vazeri/ADC-DAC-PCB/img/0.jpg

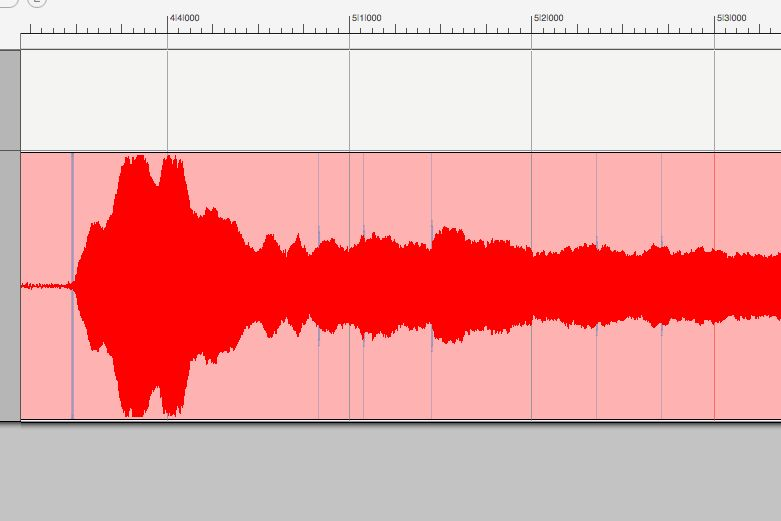
img/0.jpg
