vazeri/ADC-DAC-PCB/img/9.jpg

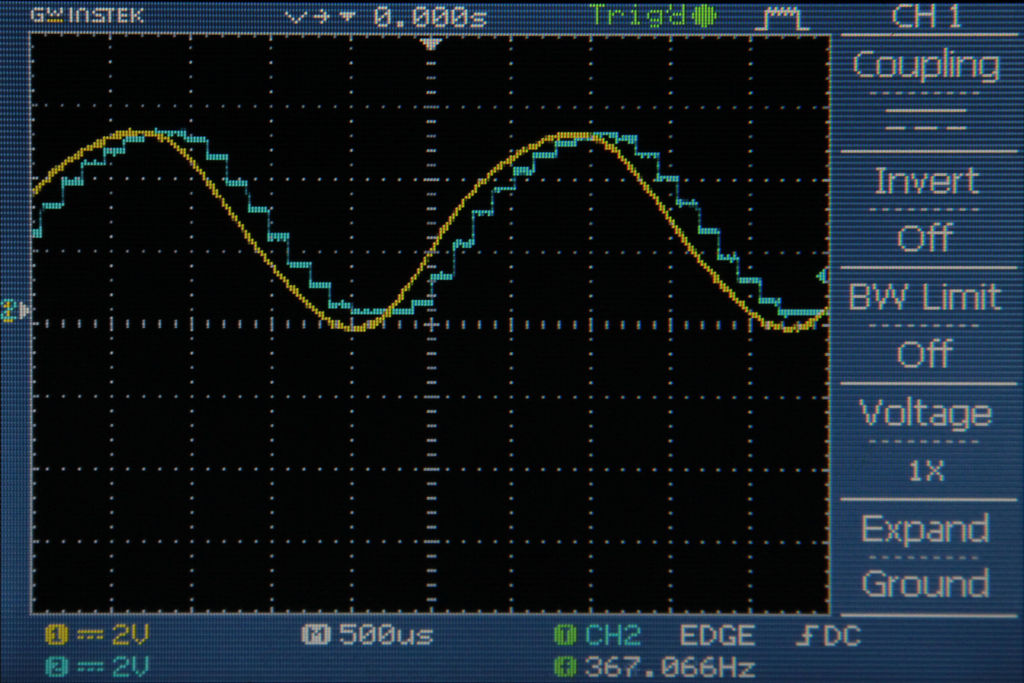
img/9.jpg
