vazeri/ADC-DAC-PCB/img/20k.jpg

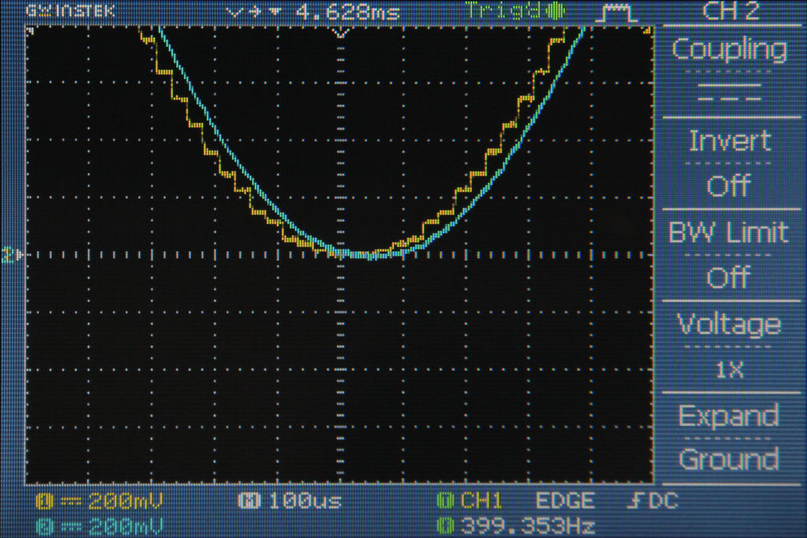
img/20k.jpg
