vazeri/ADC-DAC-PCB/img/23.JPG

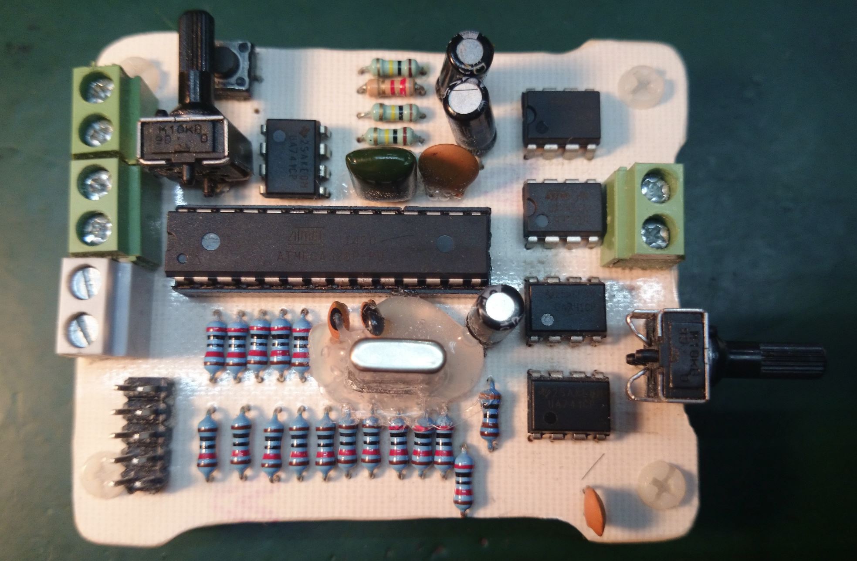
img/23.JPG
