vazeri/ADC-DAC-PCB/img/54.JPG

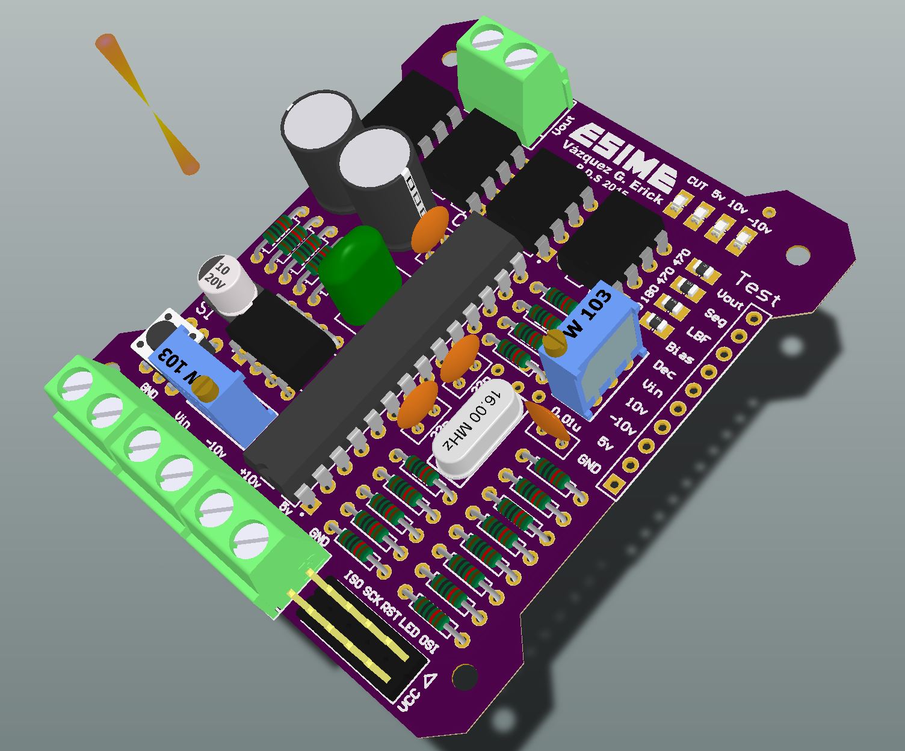
img/54.JPG
