vazeri/ADC-DAC-PCB/img/1234.JPG

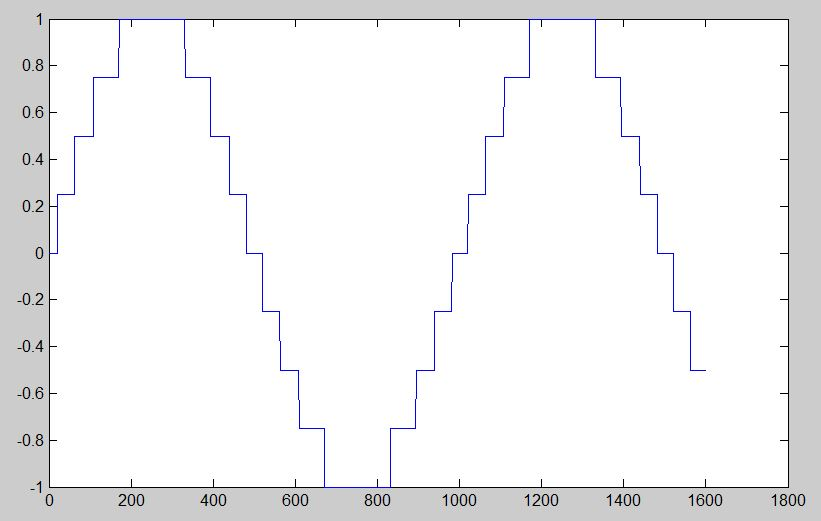
img/1234.JPG
