vazeri/ADC-DAC-PCB/img/2014-11-20 16.28.38.jpg

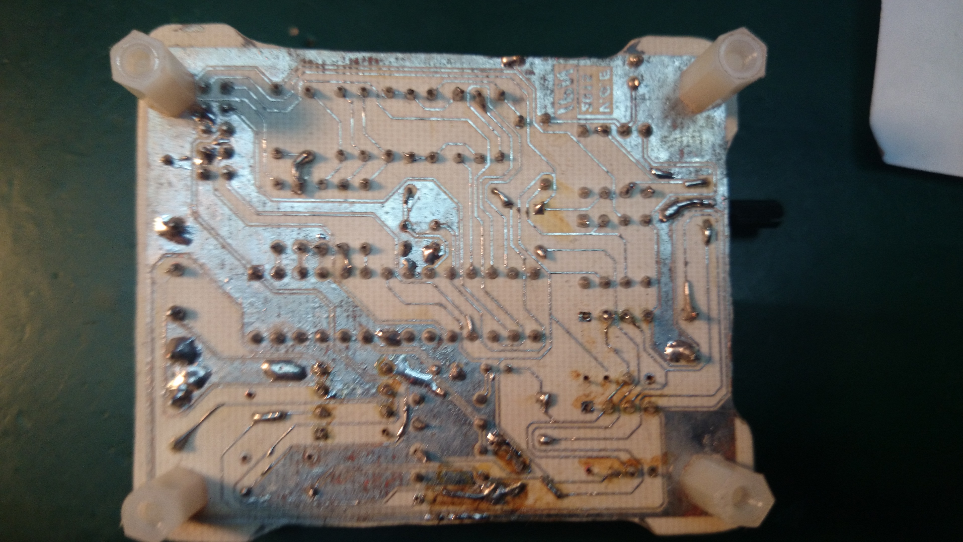
img/2014-11-20 16.28.38.jpg
