vazeri/ADC-DAC-PCB/img/2014-12-18 16.26.15.jpg

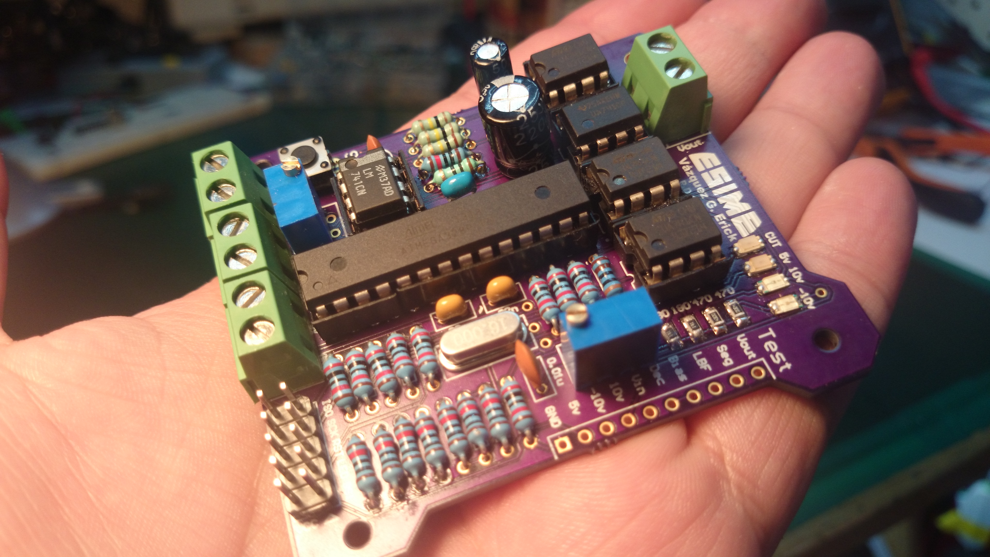
img/2014-12-18 16.26.15.jpg
