vazeri/ADC-DAC-PCB/img/1223312.JPG

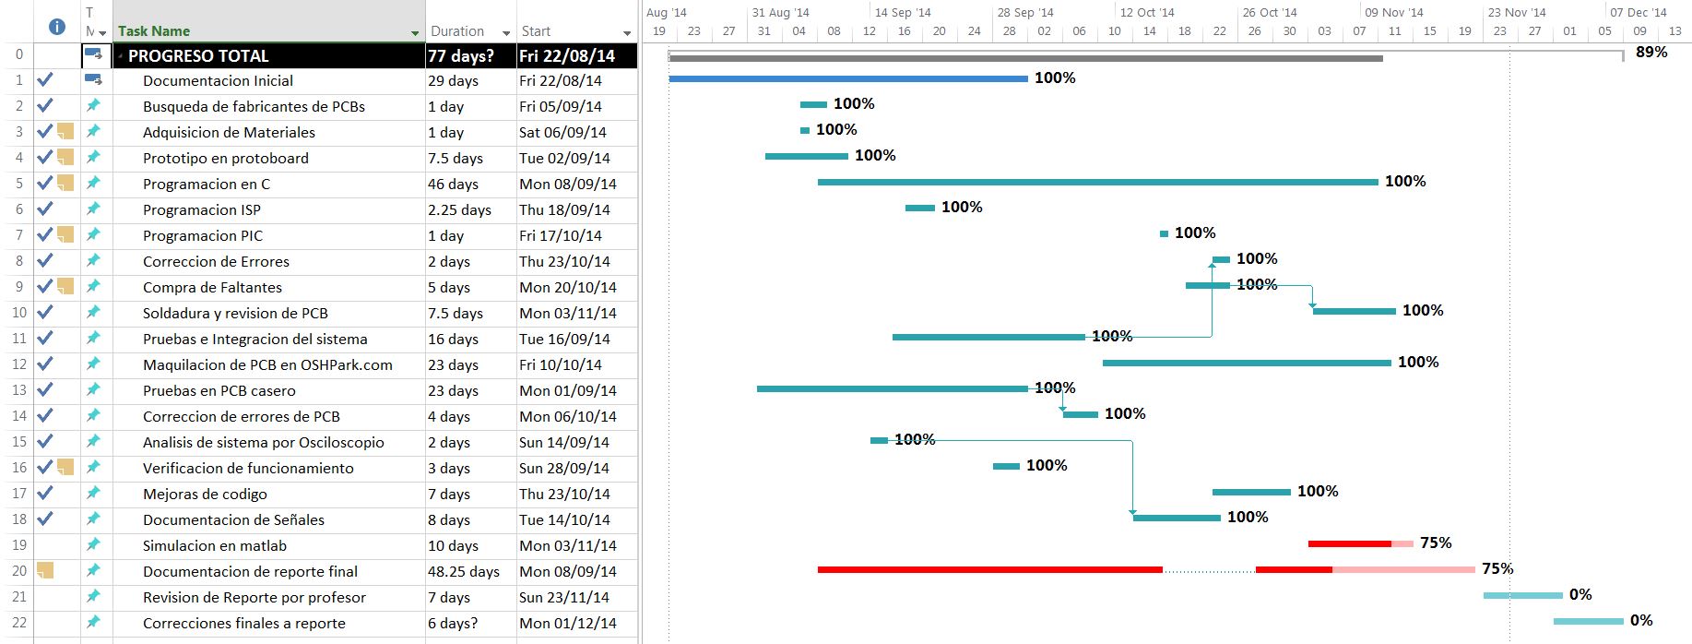
img/1223312.JPG
