vazeri/ADC-DAC-PCB/img/analog.JPG

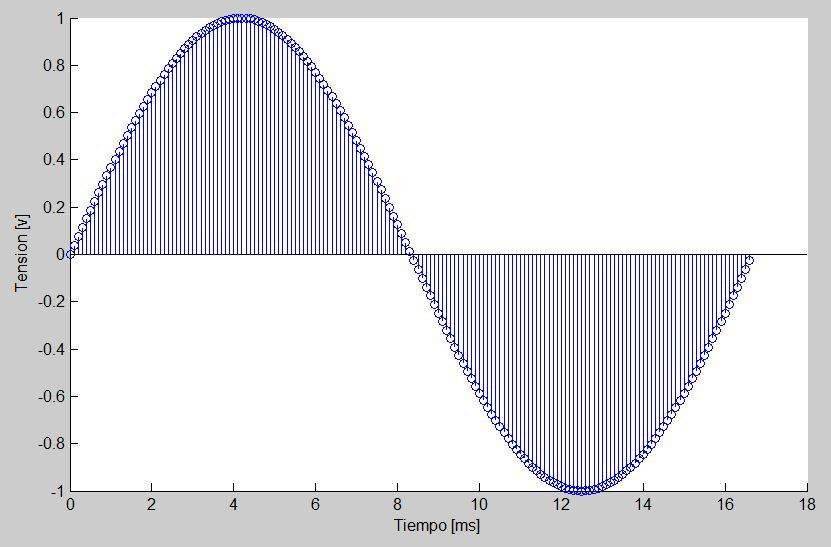
img/analog.JPG
