vazeri/ADC-DAC-PCB/img/AVR.png

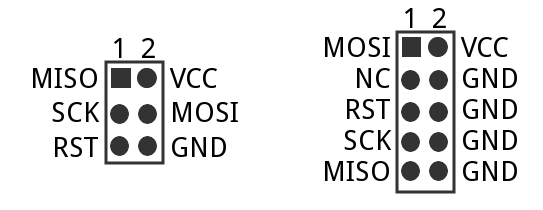
img/AVR.png
