vazeri/ADC-DAC-PCB/img/cto.JPG

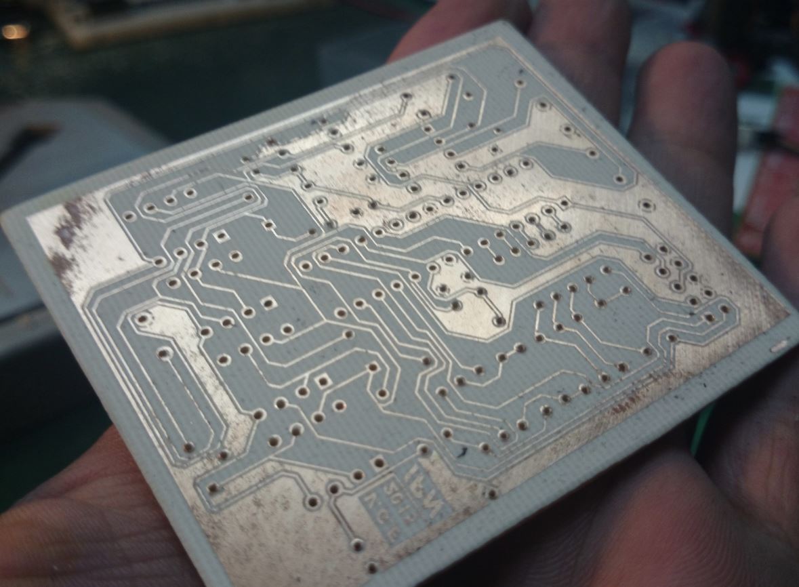
img/cto.JPG
