vazeri/ADC-DAC-PCB/img/dig.JPG

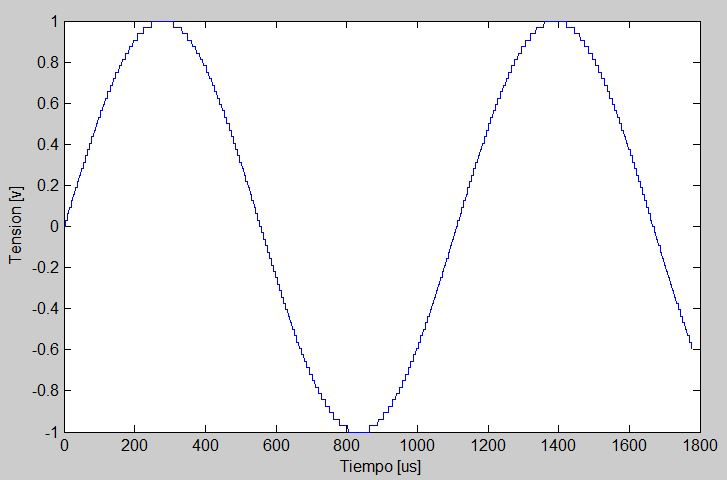
img/dig.JPG
