vazeri/ADC-DAC-PCB/img/IMG-20141107-WA0000.jpeg

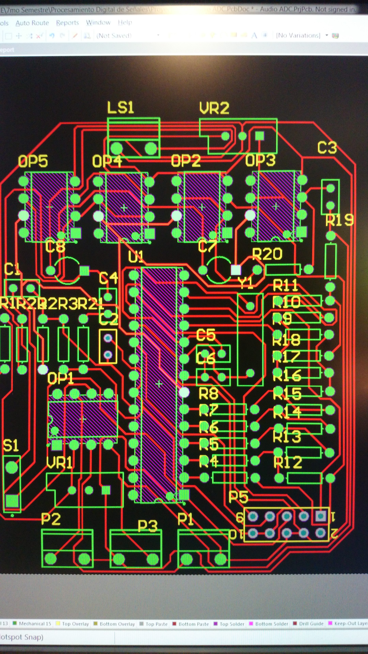
img/IMG-20141107-WA0000.jpeg
