vazeri/ADC-DAC-PCB/img/IMG-20141107-WA0002.jpeg

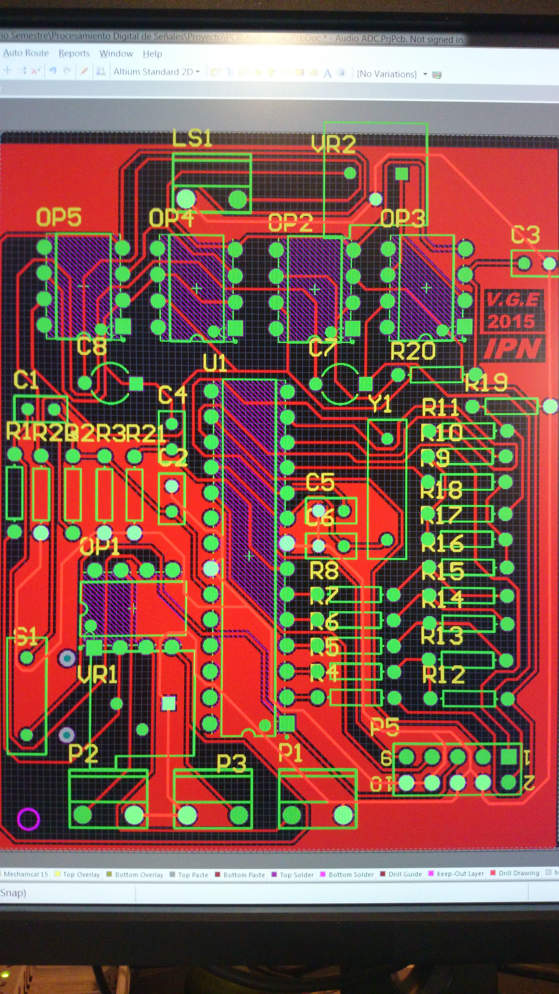
img/IMG-20141107-WA0002.jpeg
