vazeri/ADC-DAC-PCB/img/IMG-20141217-WA0004.jpeg

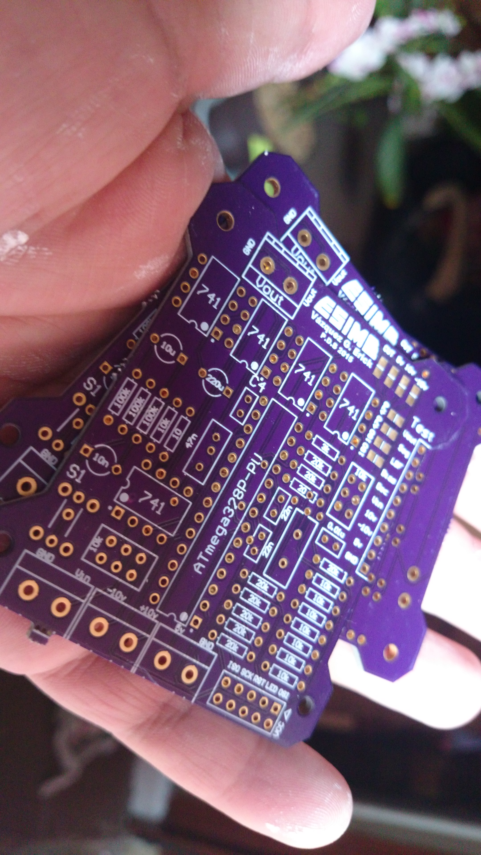
img/IMG-20141217-WA0004.jpeg
