vazeri/ADC-DAC-PCB/img/m2.JPG

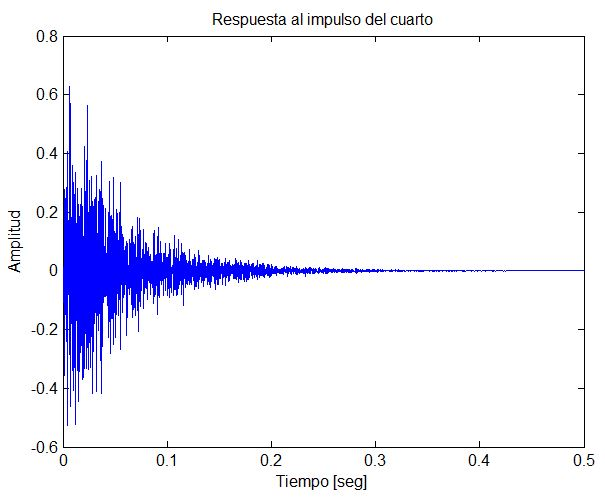
img/m2.JPG
