vazeri/ADC-DAC-PCB/img/m4.JPG

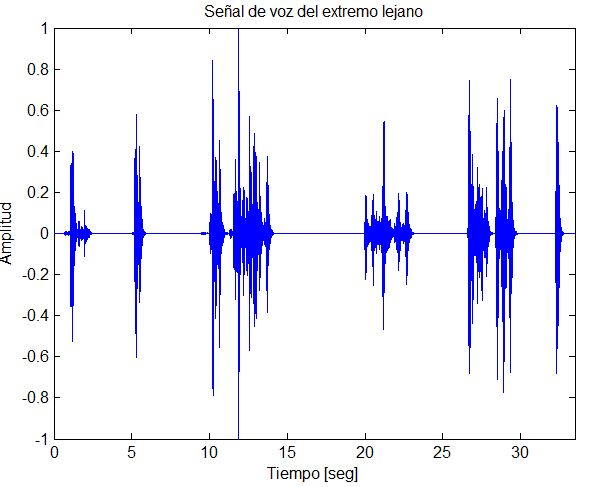
img/m4.JPG
