vazeri/ADC-DAC-PCB/img/m5.JPG

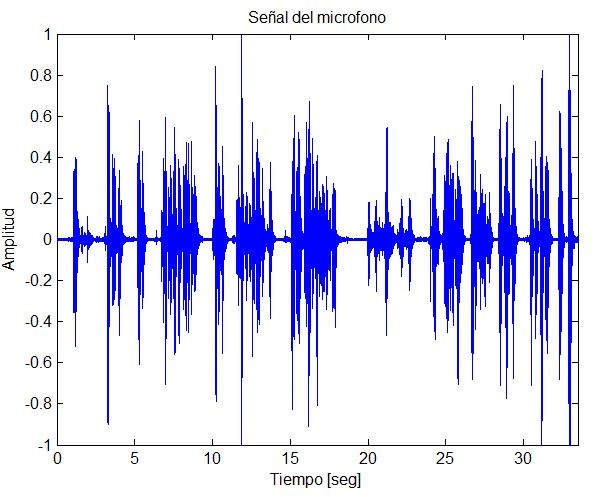
img/m5.JPG
