vazeri/ADC-DAC-PCB/img/m6.JPG

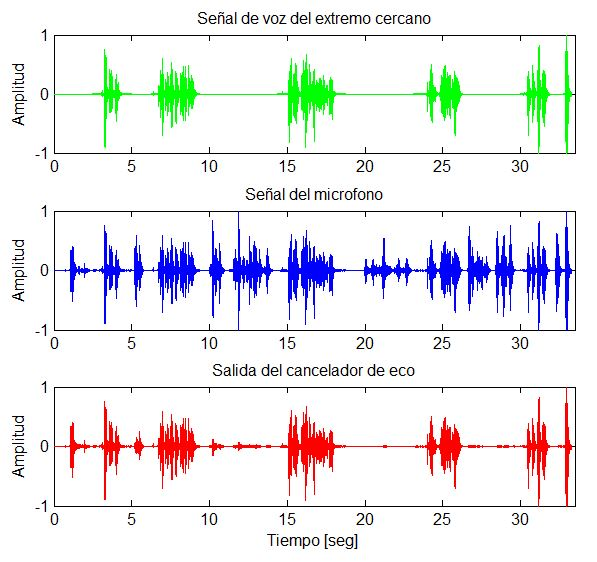
img/m6.JPG
