vazeri/ADC-DAC-PCB/img/m7.JPG

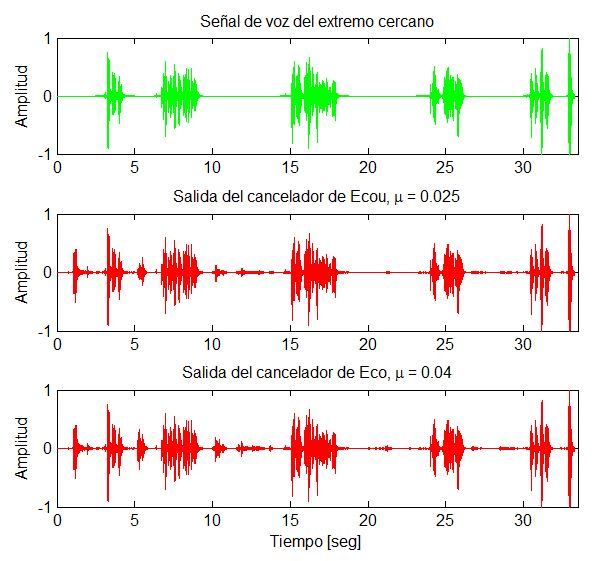
img/m7.JPG
