vazeri/ADC-DAC-PCB/img/m9.JPG

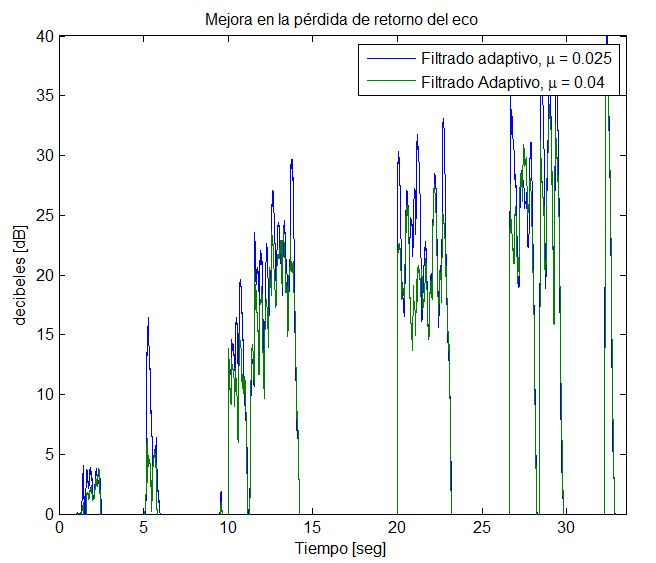
img/m9.JPG
