vazeri/ADC-DAC-PCB/img/mat.JPG

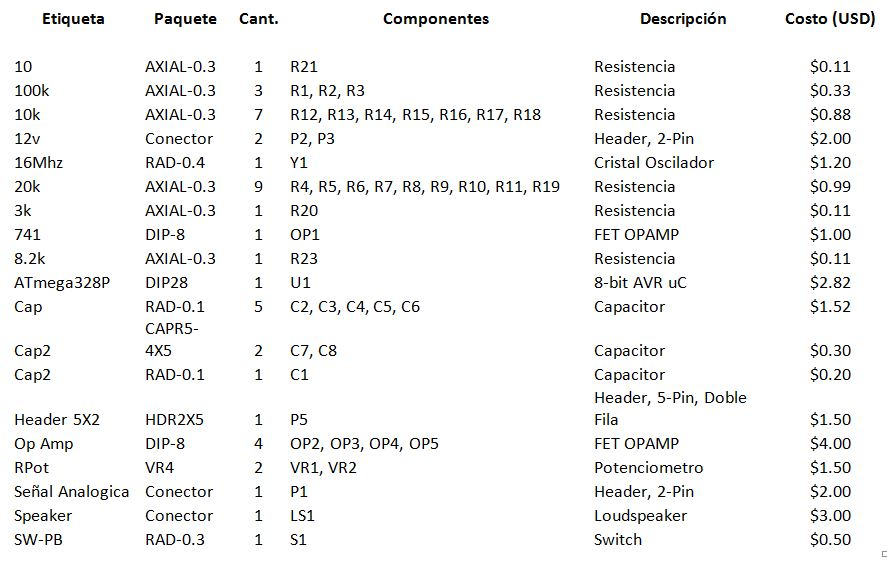
img/mat.JPG
