vazeri/ADC-DAC-PCB/img/mx.JPG

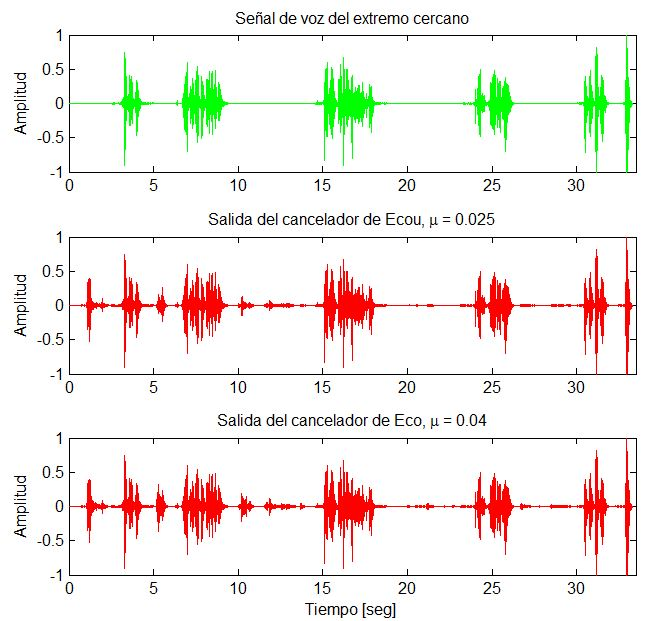
img/mx.JPG
