vazeri/ADC-DAC-PCB/img/offset.jpg

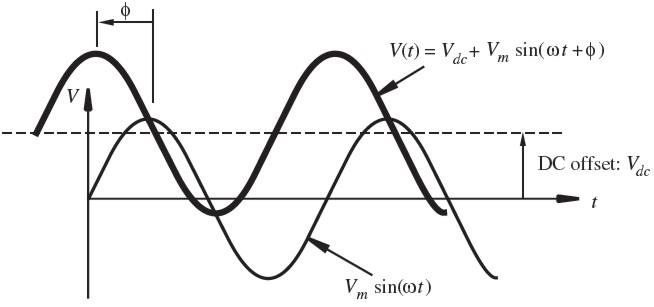
img/offset.jpg
