vazeri/ADC-DAC-PCB/img/PCB.jpg

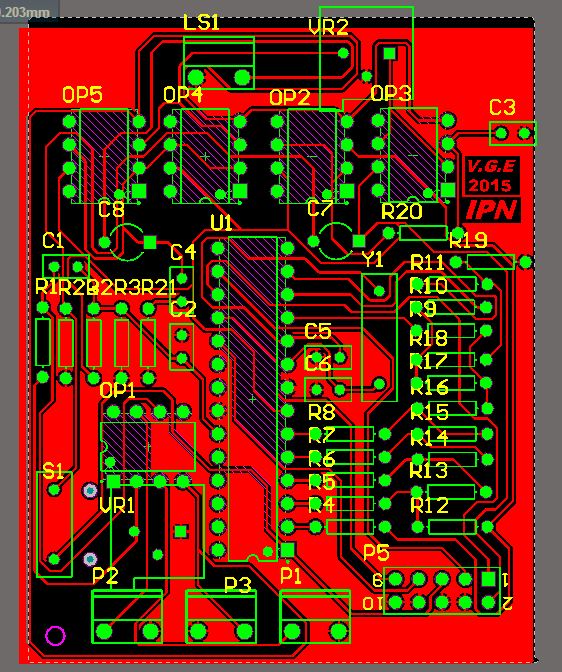
img/PCB.jpg
