vazeri/ADC-DAC-PCB/img/simulacion.jpg

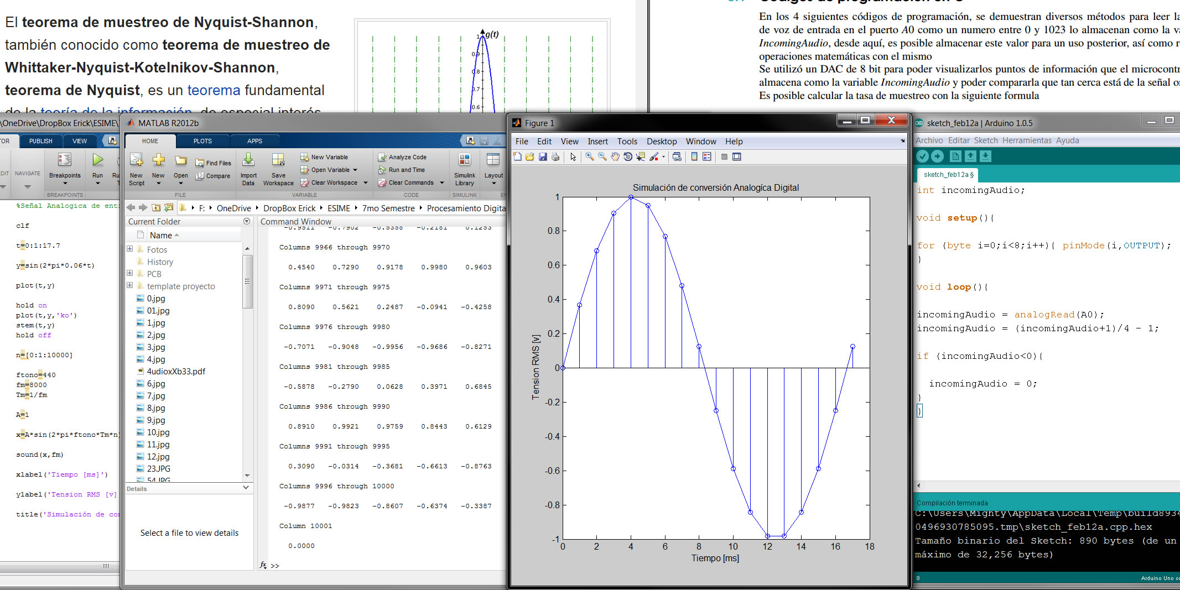
img/simulacion.jpg
