vazeri/ADC-DAC-PCB/img/tarjeta.jpg

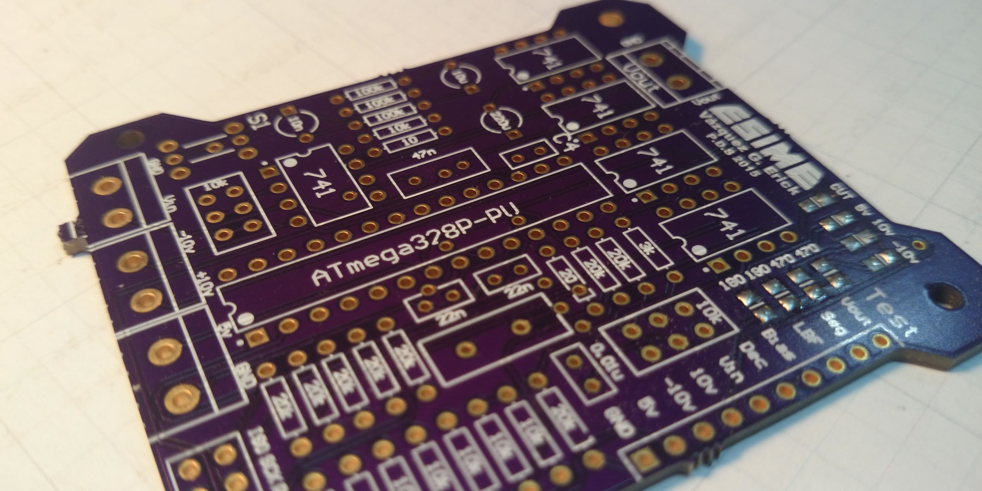
img/tarjeta.jpg
