vazeri/ADC-DAC-PCB/Altium/User Library-LED SMD0805.step

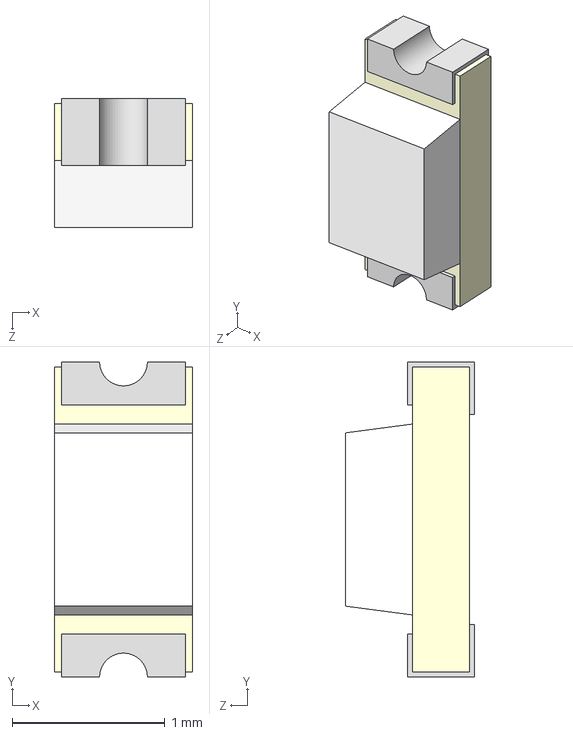
[picture p67: CAD file, 2018-01-22]
Altium/User Library-LED SMD0805.step
0.906 x 2.06 x 0.844 mm
