vazeri/ADC-DAC-PCB/Altium/User Library-Bourns 3362P.step

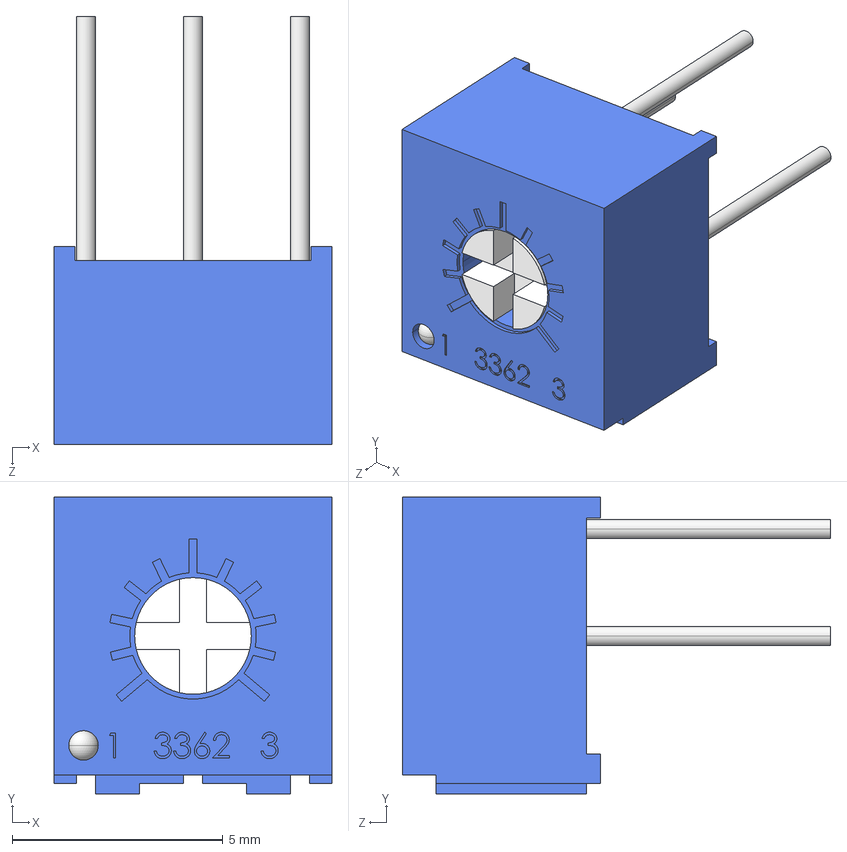
[picture p68: CAD file, 2018-01-22]
Altium/User Library-Bourns 3362P.step
6.60 x 7.05 x 10.2 mm
