vazeri/ADC-DAC-PCB/Altium/User Library-Cap12_5x25.STEP

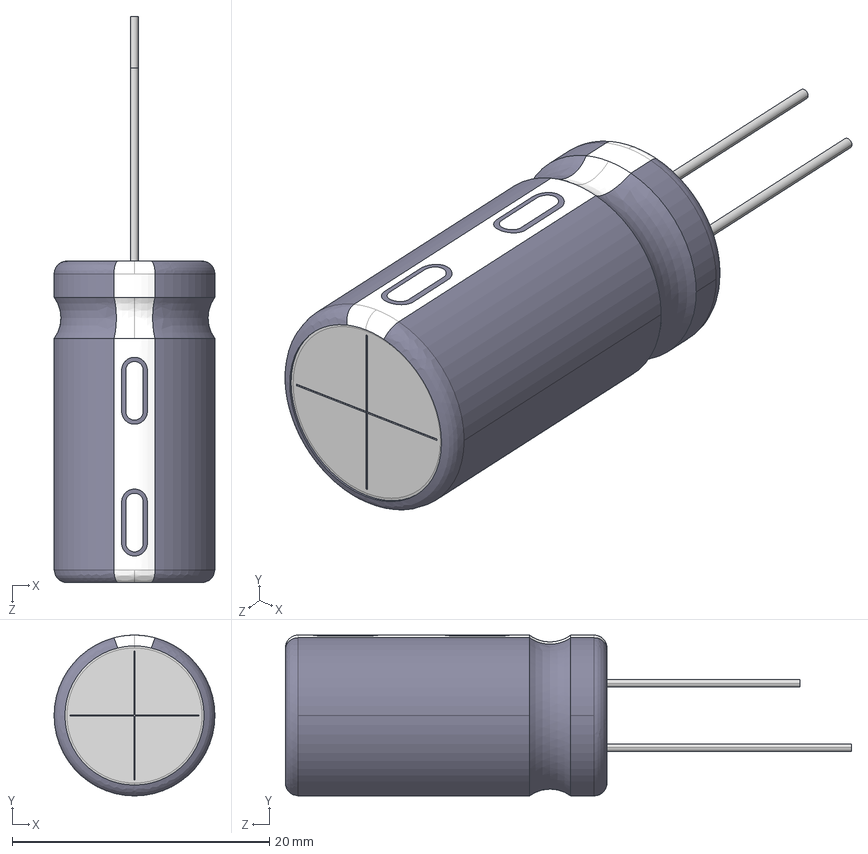
[picture p69: CAD file, 2018-01-22]
Altium/User Library-Cap12_5x25.STEP
12.5 x 12.5 x 44.0 mm
User Library-Cap12.5x25_1_1
User Library-Cap12.5x25_2_1
User Library-Cap12.5x25_3_1
User Library-Cap12.5x25_4_1
User Library-Cap12.5x25_5_1
User Library-Cap12.5x25_6_1
User Library-Cap12.5x25_7_1
User Library-Cap12.5x25_8_1
User Library-Cap12.5x25_9_1
User Library-Cap12.5x25_10_1
