vazeri/ADC-DAC-PCB/Altium/47n.step

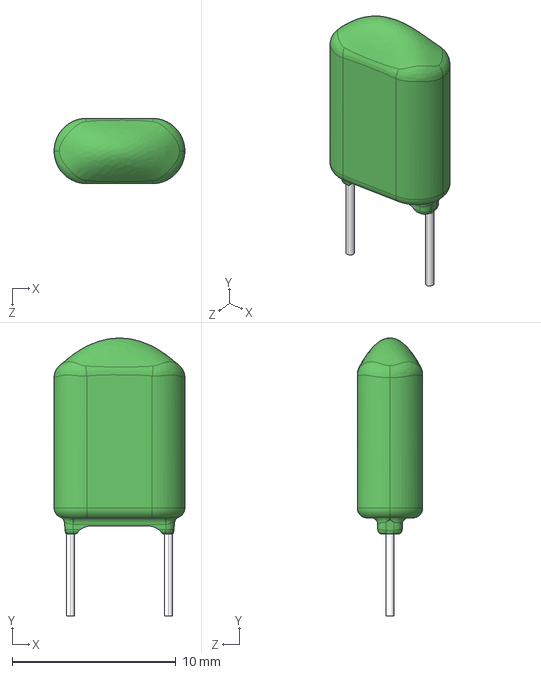
[picture p70: CAD file, 2018-01-22]
Altium/47n.step
8.00 x 17.0 x 4.00 mm
