vazeri/ADC-DAC-PCB/Altium/User Library-DIP8test.STEP

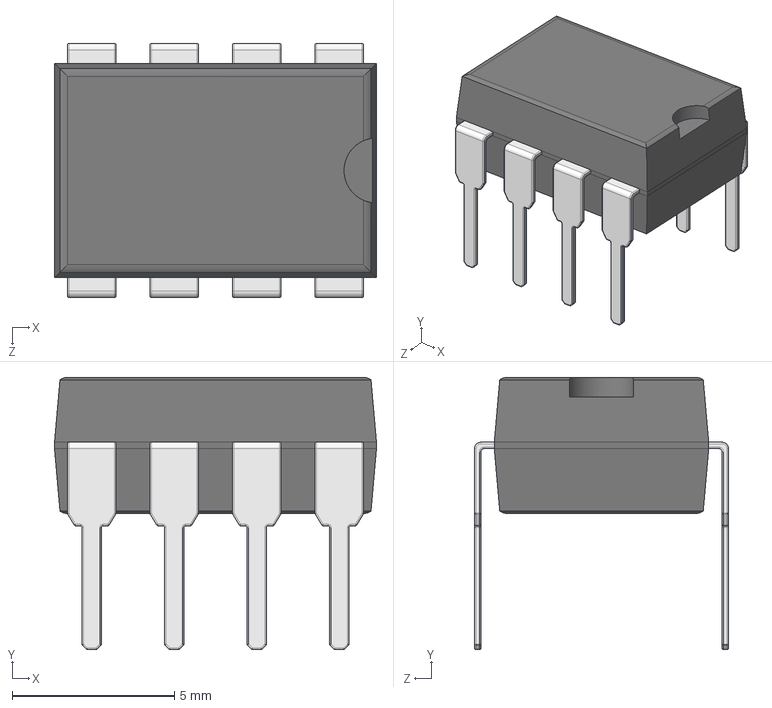
[picture p71: CAD file, 2018-01-22]
Altium/User Library-DIP8test.STEP
9.91 x 8.38 x 7.82 mm
User Library-DIP8test_K_X_F6rper DIP8_1
User Library-DIP8test_Pins Narrow_1 x 8
