vazeri/ADC-DAC-PCB/Altium/Terminal Block.stp

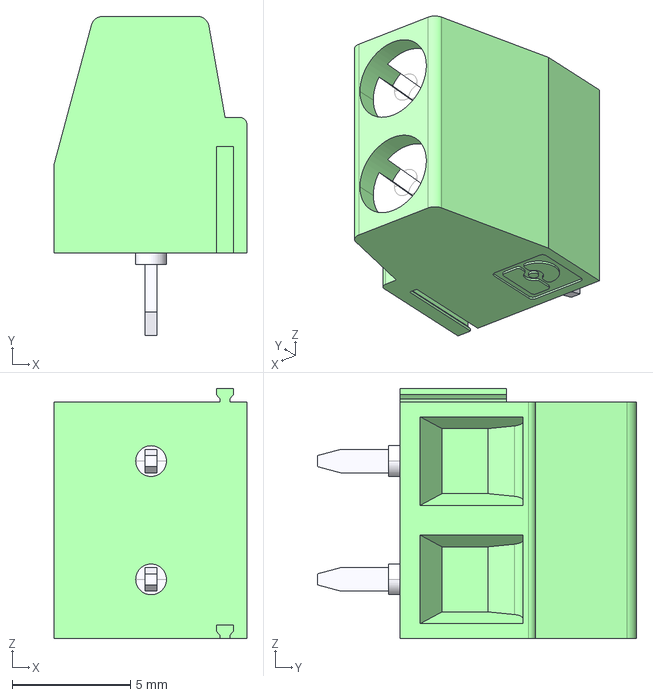
[picture p72: CAD file, 2018-01-22]
Altium/Terminal Block.stp
8.15 x 13.5 x 10.6 mm
