vazeri/ADC-DAC-PCB/Altium/CircuitWorks-REDLED.step

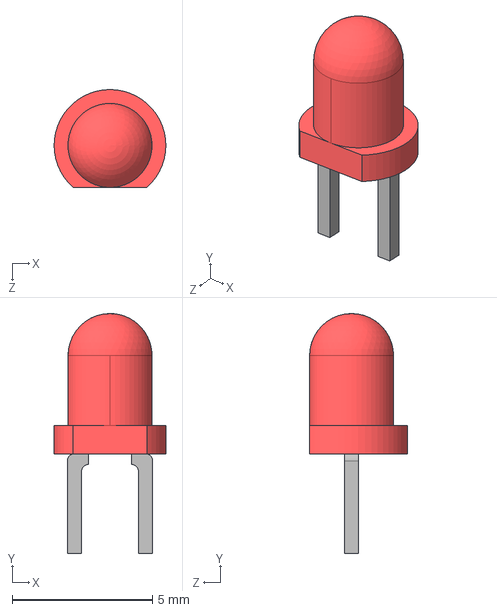
[picture p73: CAD file, 2018-01-22]
Altium/CircuitWorks-REDLED.step
3.99 x 8.56 x 3.49 mm
