vazeri/ADC-DAC-PCB/img/PRUEBAS.jpg

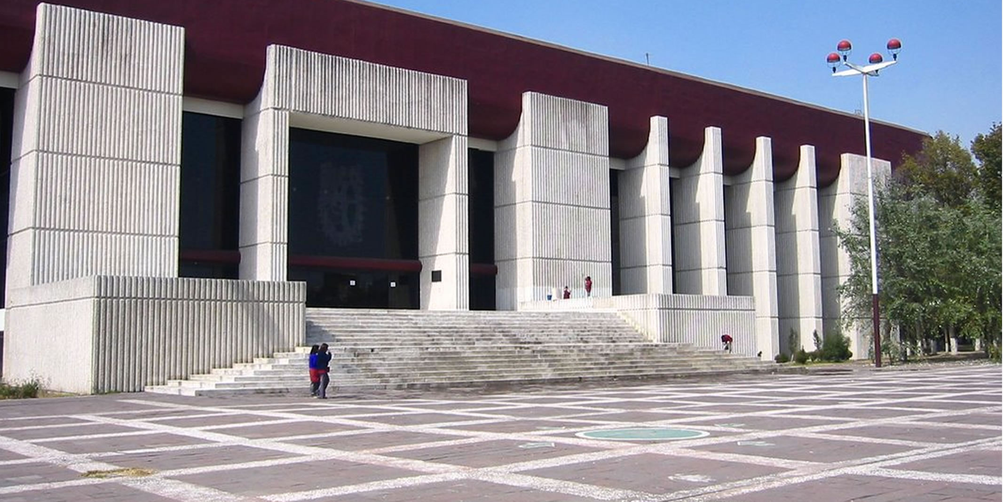
img/PRUEBAS.jpg
